hackrockcity/domeFirmware/python_host/domelistener.py

import socket
import time
import Queue
import multiprocessing
import LedStrips

# UDP settings
host = "0.0.0.0"
port = 58082
buffer_size = 200000

# Image settings
image_height = 160
image_width = 24

# Serial port settings
strip_names = [
	['/dev/ttyACM0', 0],
	['/dev/ttyACM1', 16],
	['/dev/ttyACM2', 8],
]

class threadedLedStrips(multiprocessing.Process):

	def __init__(self, port_name, offset,
			data_array, new_data_event, draw_event):
		self.port_name = port_name
		self.offset = offset

		self.strip = LedStrips.LedStrips(image_width, offset)
		self.strip.connect(port_name)

		self.data = data_array
		self.new_data_event = new_data_event
		self.draw_event = draw_event

		multiprocessing.Process.__init__(self, target=self.run)

	def run(self):
		while True:
			# Wait for new data, then load it into the strip
#			print " %i wait for data"%self.offset
			self.new_data_event.wait()
#			print " %i got data"%self.offset
			self.strip.load_data(self.data)

			# Wait for a write event, then signal the frame to flip over
#			print " %i wait for draw--"%self.offset
			self.draw_event.wait()
#			print " %i got draw--"%self.offset
			self.strip.flip()


sock = socket.socket(socket.AF_INET, socket.SOCK_DGRAM)
sock.bind((host,port))

strips = []

new_data_event = multiprocessing.Event()
draw_event = multiprocessing.Event()
image_data = multiprocessing.Array('c', image_width*image_height*3)

for strip_name in strip_names:
	strip = threadedLedStrips(strip_name[0], strip_name[1],
		image_data, new_data_event, draw_event)
	strip.start()
	strips.append(strip)

start_time = time.time()
frame_count = 0
while 1:
	data, addr = sock.recvfrom(buffer_size)
        update_start_time = time.time()
	
	if not data:
		print "no data."
		continue

	if data[0] != '\x01':
		print "bad header, expected=%i, got=%i"%(1, ord(data[0]))
		continue

	expected_length = image_width*image_height*3+1
	if len(data) != expected_length:
		print "bad data length, expected %i, got %i"%(expected_length, len(data))
		continue

#	print "Send draw"
	send_draw_start_time = time.time()
	# Clock out the previous frame
	new_data_event.clear()
	draw_event.set()
	send_draw_time = time.time() - send_draw_start_time

	# Load in the next frame
	load_frame_start_time = time.time()
	image_data[:] = data[1:]
#	for pos in range(0, image_width*image_height*3):
#		image_data[pos] = data[pos+1]
	load_frame_time = time.time() - load_frame_start_time

#	print "Send data--"
	send_data_start_time = time.time()
	draw_event.clear()
	new_data_event.set()
	send_data_time = time.time() - send_data_start_time

	frame_count = (frame_count + 1) % 30
	if (frame_count == 0):
		print "Frame rate: %3.1f"%(30/(time.time() - start_time))
		start_time = time.time()
#	print 'update_time=%4.4f, send_draw=%4.4f, load_frame=%4.4f, send_data=%4.4f'%(
#		time.time() - update_start_time,
#		send_draw_time,
#		load_frame_time,
#		send_data_time
#		)
